egillmilan/MPad2040_V1/Silkscreen_art/output_images/baboonDotsSquare.bmp

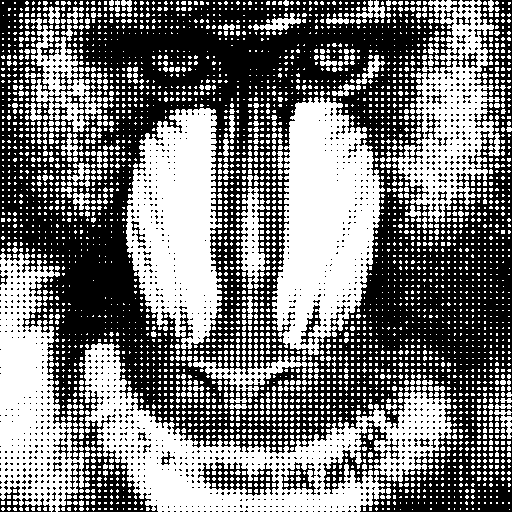
Silkscreen_art/output_images/baboonDotsSquare.bmp
