egillmilan/MPad2040_V1/Silkscreen_art/output_images/MPad2040_front.png

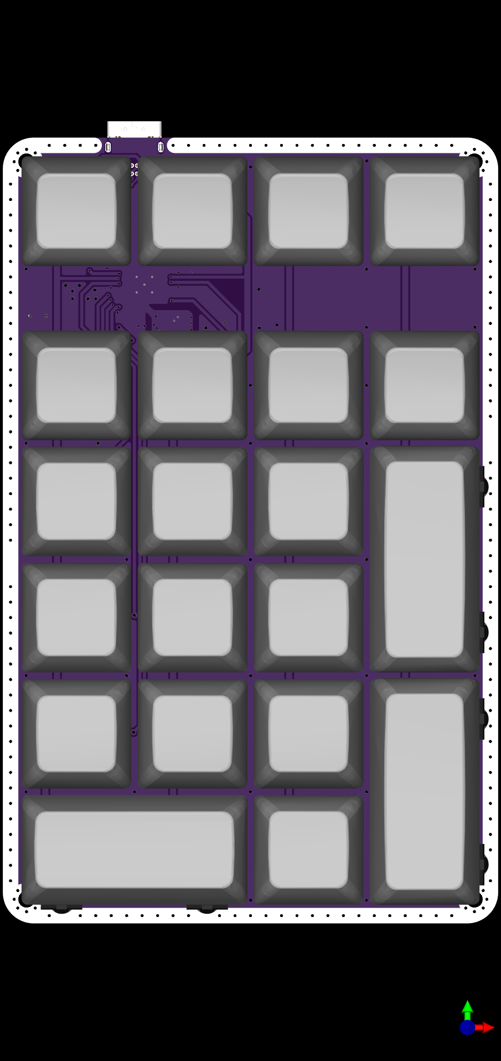
Silkscreen_art/output_images/MPad2040_front.png
