egillmilan/MPad2040_V1/Silkscreen_art/output_images/waveFloydSteinbergDots.bmp

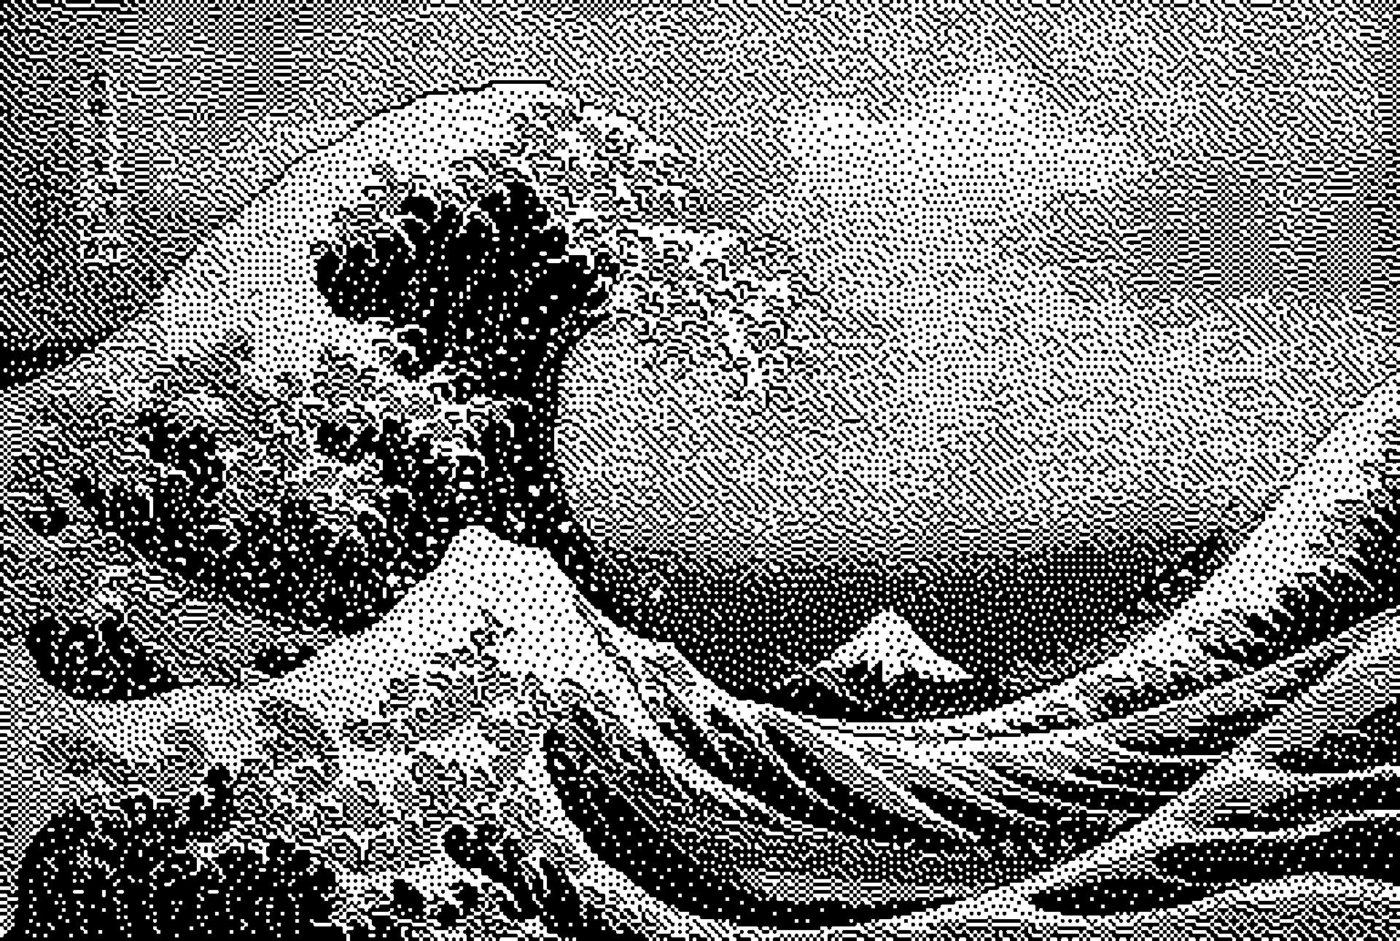
Silkscreen_art/output_images/waveFloydSteinbergDots.bmp
