egillmilan/MPad2040_V1/Silkscreen_art/saturn/edited/saturn12_e.bmp

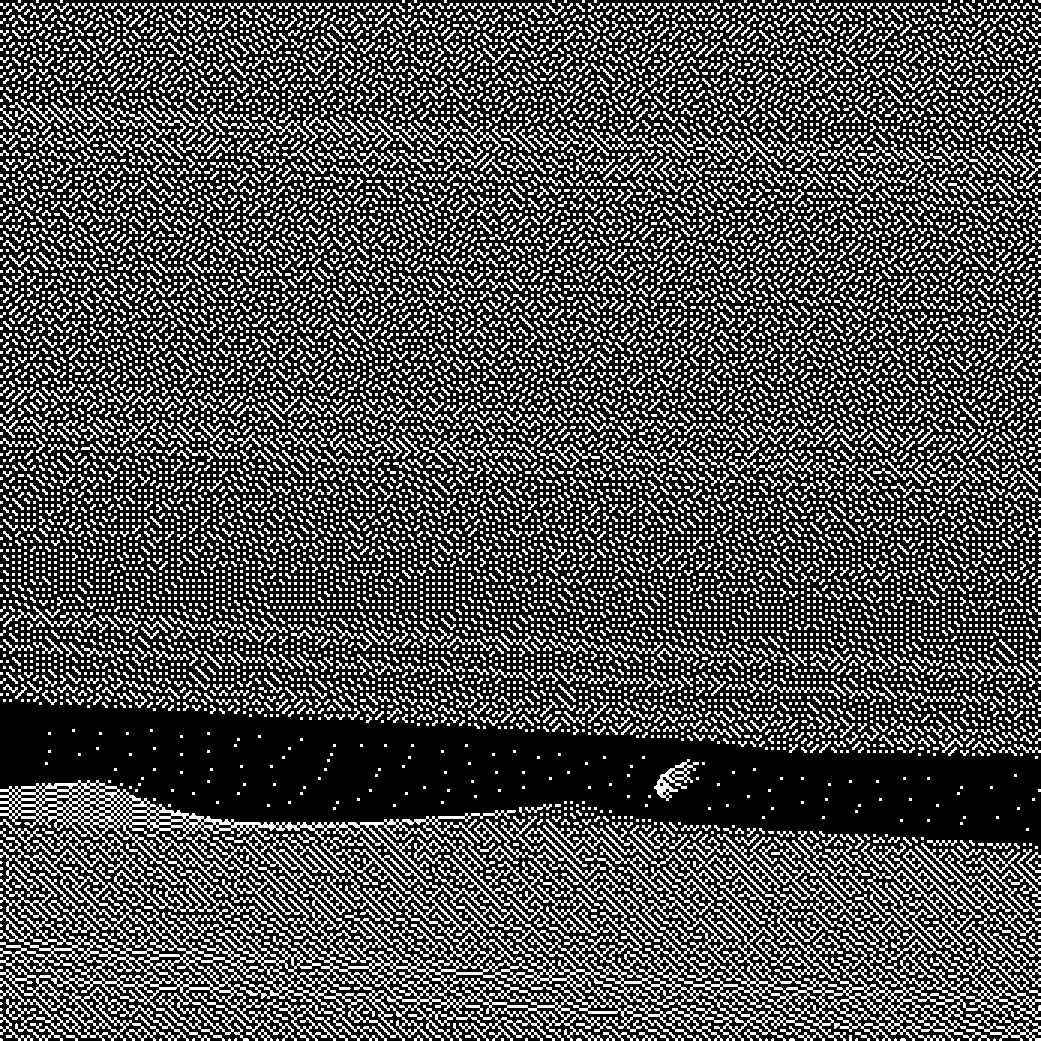
Silkscreen_art/saturn/edited/saturn12_e.bmp
