egillmilan/MPad2040_V1/Silkscreen_art/saturn/edited/saturn14_e.bmp

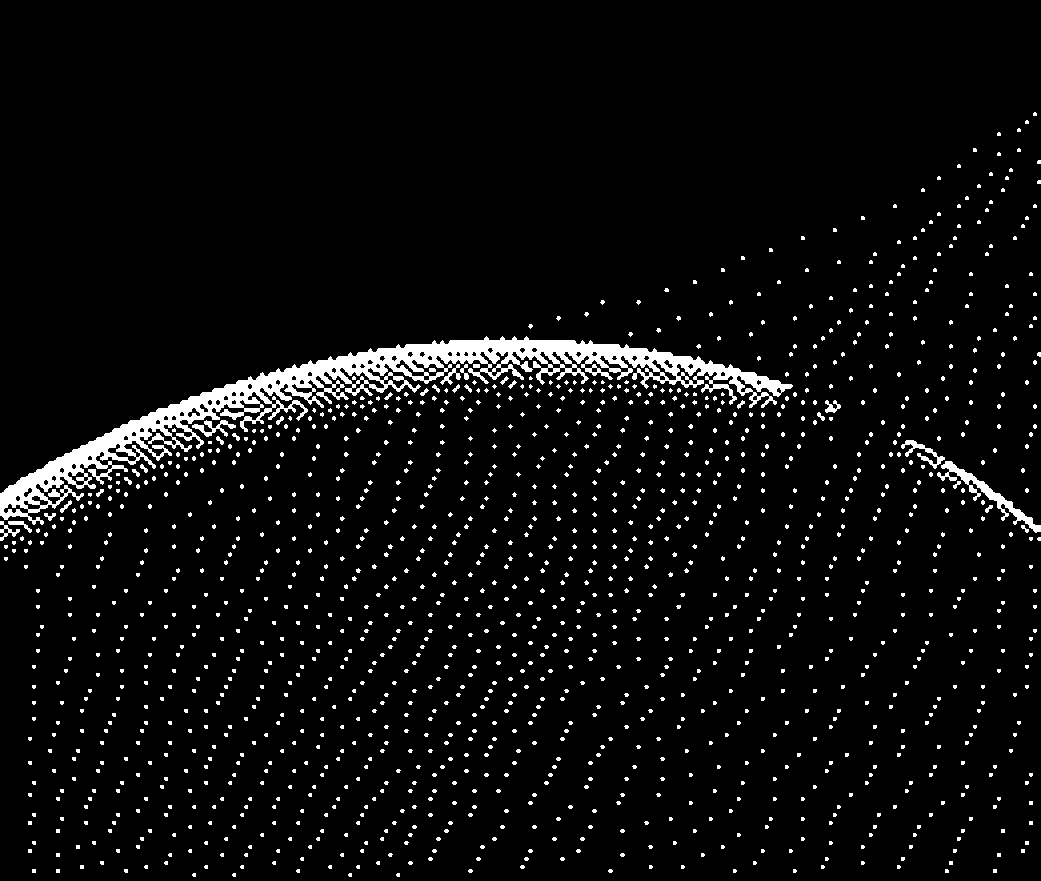
Silkscreen_art/saturn/edited/saturn14_e.bmp
