egillmilan/MPad2040_V1/Silkscreen_art/saturn/saturn12.jpg

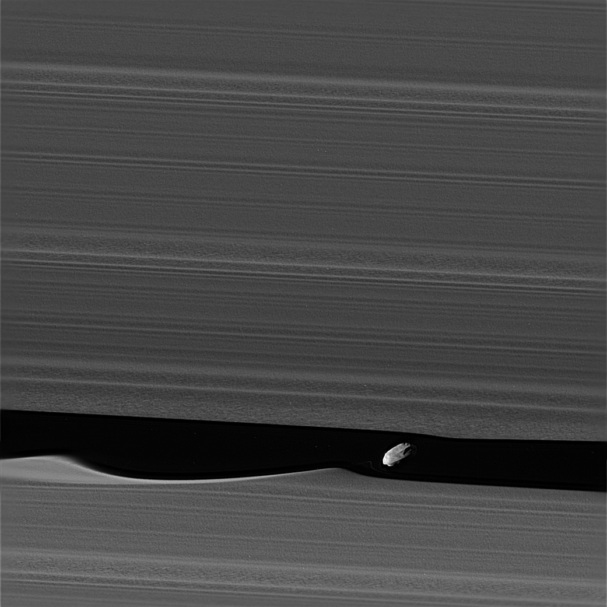
Silkscreen_art/saturn/saturn12.jpg
