egillmilan/MPad2040_V1/Silkscreen_art/saturn/saturn14.jpg

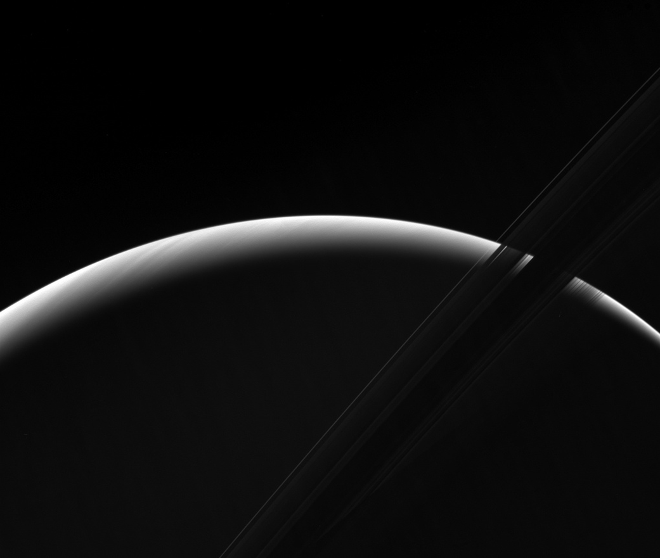
Silkscreen_art/saturn/saturn14.jpg
